rodion-bln/InkTime-Smartwatch/Images/parts3D.png

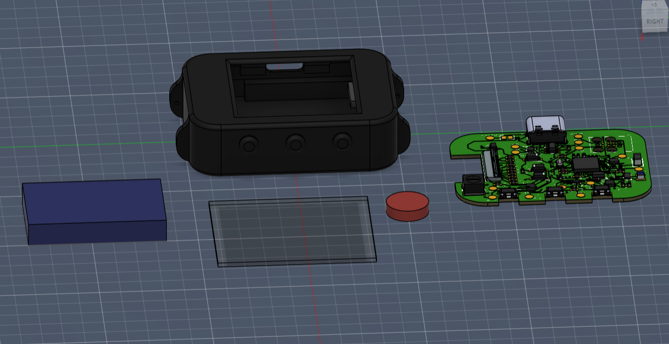
Images/parts3D.png
